EricYufengWu/SPIKExCM4/Documentation/5.jpeg

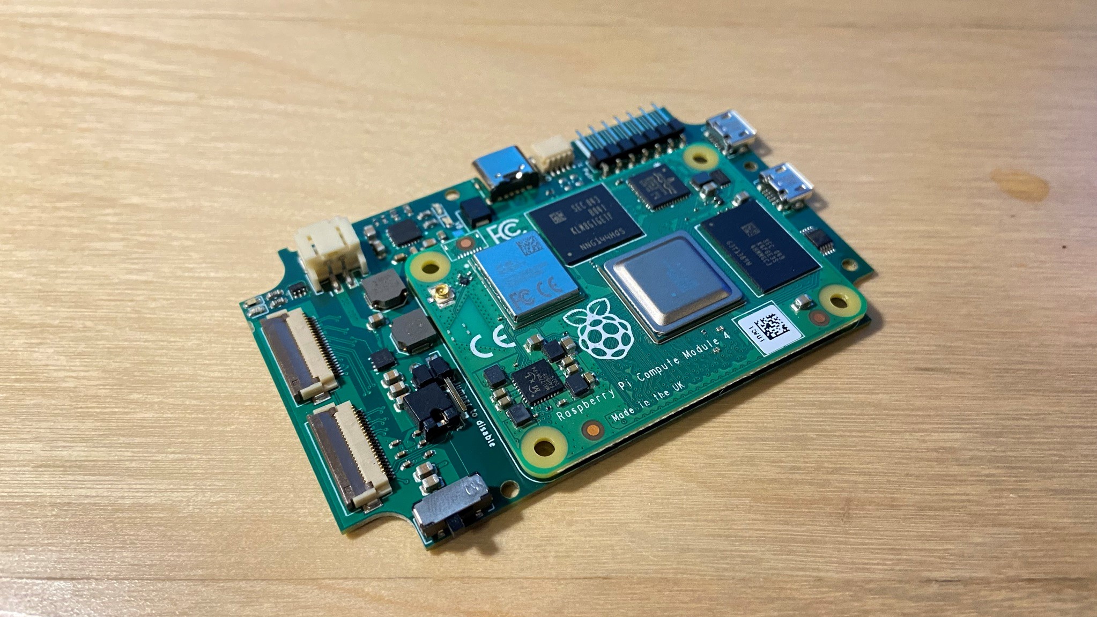
Documentation/5.jpeg
