EricYufengWu/SPIKExCM4/CAD/STEP/BQ25616RTWT.STEP

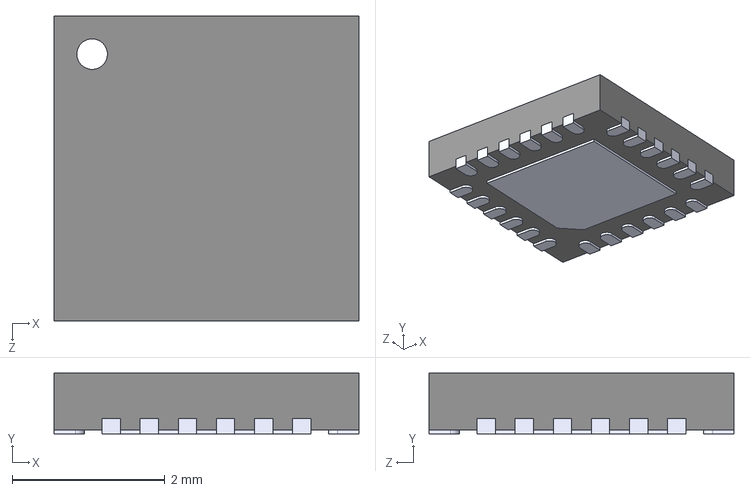
[picture p28: CAD file, 2021-06-10]
CAD/STEP/BQ25616RTWT.STEP
4.00 x 0.8 x 4.00 mm
